connorzheng97/phantom-power/docs/img/DSC_0406.jpg

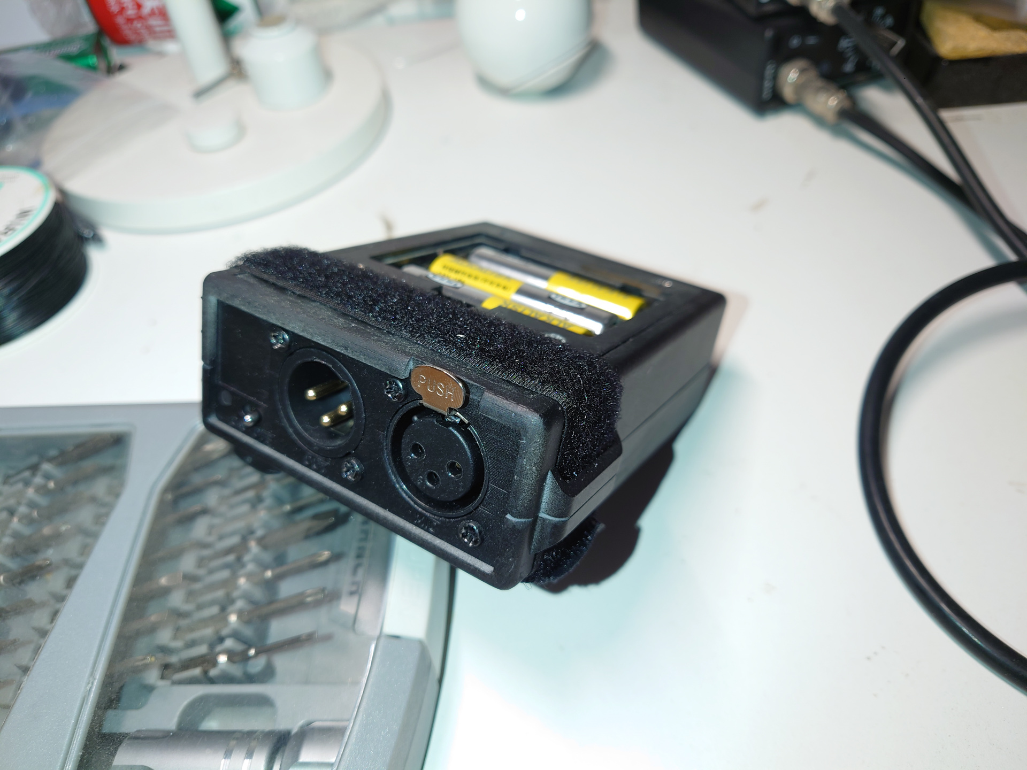
docs/img/DSC_0406.jpg
